roadsidebomb/Polybar-Minibar-3D-Print-Files/Official Releases/Polybar-Minibar v5.0 STLs/Frames/Polybar Les Paul Frame (Bottom).stl

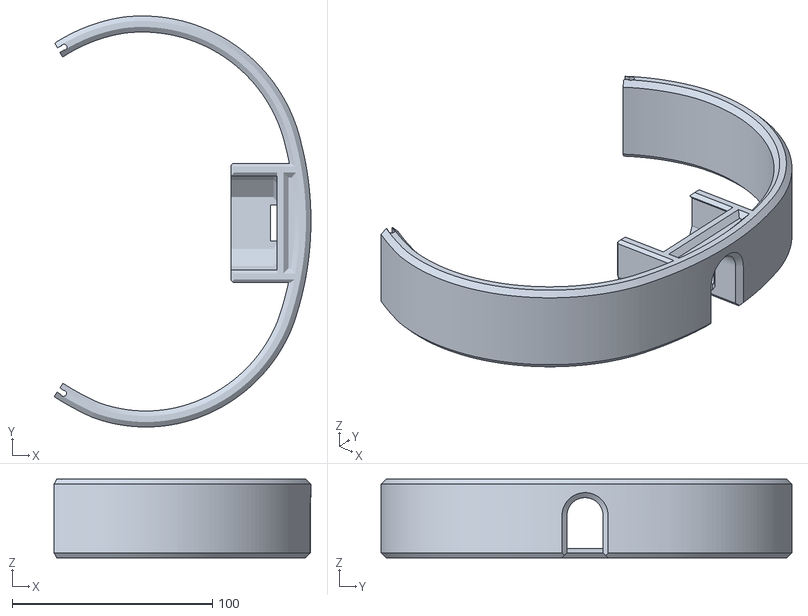
[picture p15: CAD file, 2023-04-15]
Official Releases/Polybar-Minibar v5.0 STLs/Frames/Polybar Les Paul Frame (Bottom).stl
128.2 x 205.1 x 39.4
