roadsidebomb/Polybar-Minibar-3D-Print-Files/Official Releases/Polybar-Minibar v5.0 STLs/Minibar/Minibar Strum Case (Bottom).stl

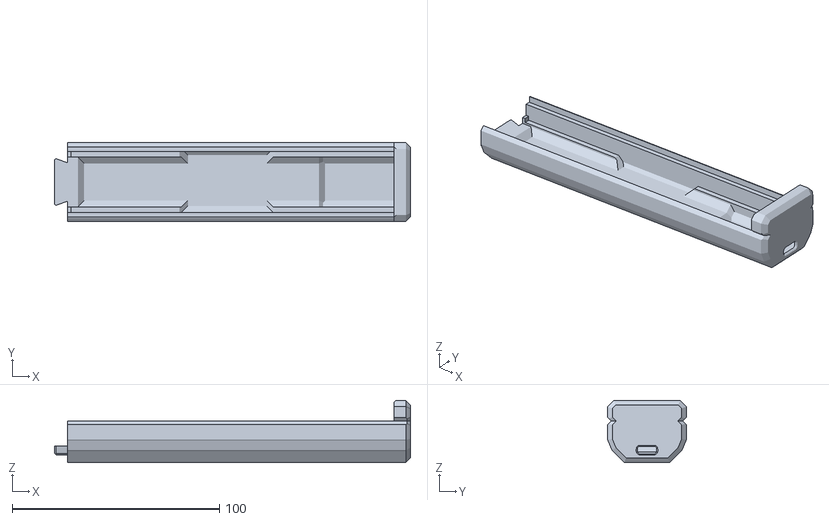
[picture p16: CAD file, 2023-04-15]
Official Releases/Polybar-Minibar v5.0 STLs/Minibar/Minibar Strum Case (Bottom).stl
171.9 x 38.0 x 30.0
