roadsidebomb/Polybar-Minibar-3D-Print-Files/Official Releases/Polybar-Minibar v5.0 STLs/Polybar/Polybar Strum Case (Bottom).stl

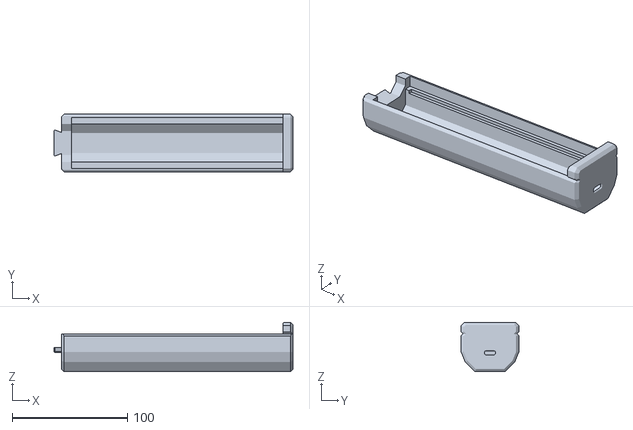
[picture p17: CAD file, 2023-04-15]
Official Releases/Polybar-Minibar v5.0 STLs/Polybar/Polybar Strum Case (Bottom).stl
207.3 x 50.0 x 42.9
