roadsidebomb/Polybar-Minibar-3D-Print-Files/Official Releases/Polybar-Minibar v5.0 STLs/Universal Parts/Large Button.stl

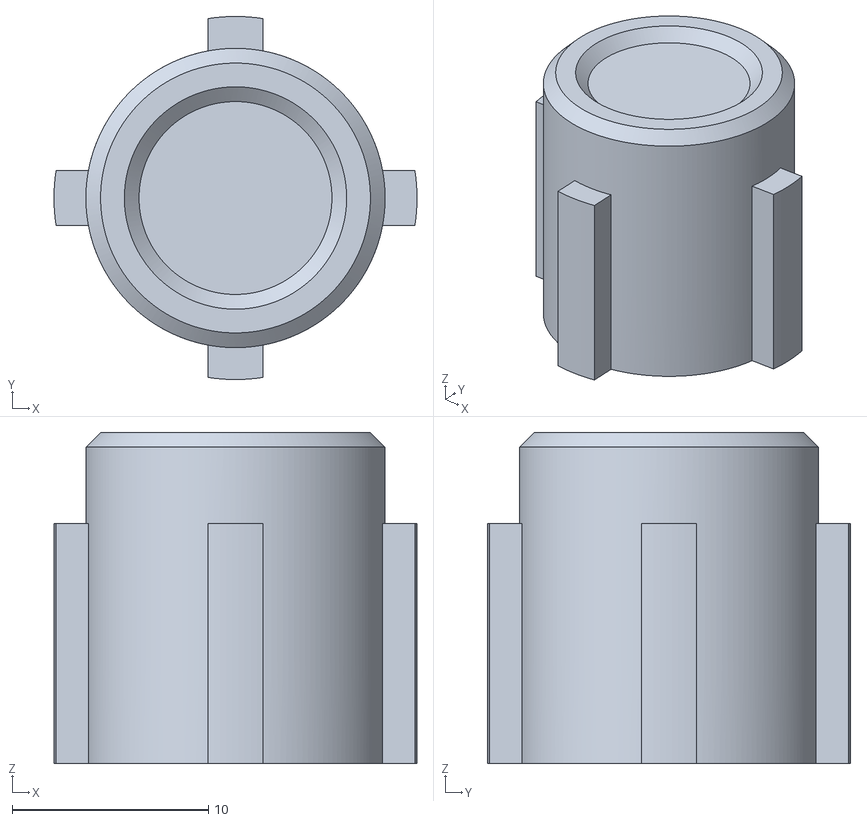
[picture p18: CAD file, 2023-04-15]
Official Releases/Polybar-Minibar v5.0 STLs/Universal Parts/Large Button.stl
18.5 x 18.5 x 16.9
