roadsidebomb/Polybar-Minibar-3D-Print-Files/Official Releases/Polybar-Minibar v5.0 STLs/Universal Shells/Fret Shell (Top).stl

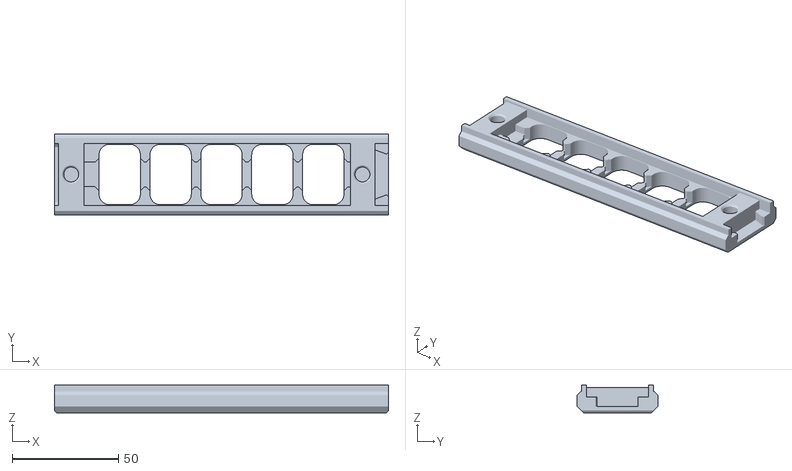
[picture p19: CAD file, 2023-04-15]
Official Releases/Polybar-Minibar v5.0 STLs/Universal Shells/Fret Shell (Top).stl
157.5 x 38.0 x 13.0
