roadsidebomb/Polybar-Minibar-3D-Print-Files/Official Releases/Polybar-Minibar v5.0 STLs/Alternates/5. Large Button/Large Button - .25 down.stl

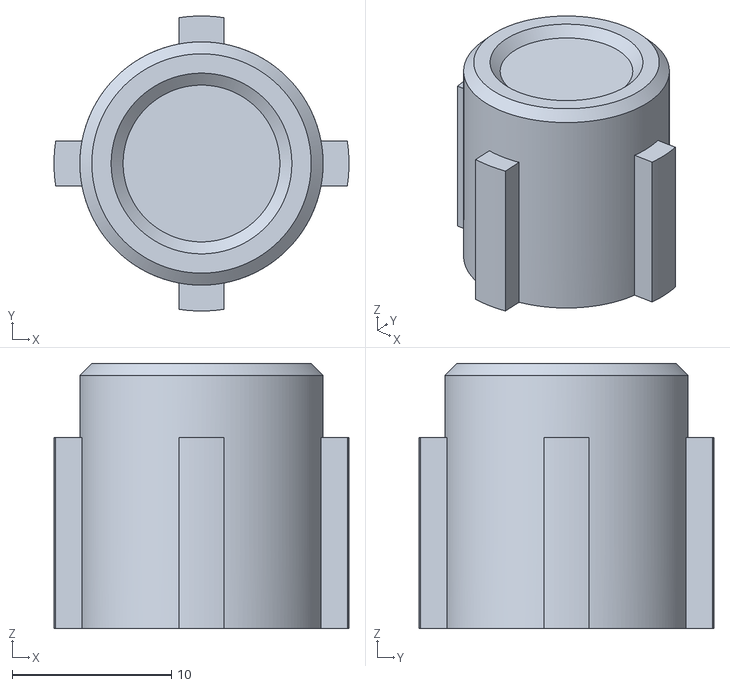
[picture p20: CAD file, 2023-04-15]
Official Releases/Polybar-Minibar v5.0 STLs/Alternates/5. Large Button/Large Button - .25 down.stl
18.5 x 18.5 x 16.6
