roadsidebomb/Polybar-Minibar-3D-Print-Files/Official Releases/Polybar-Minibar v5.0 STLs/Alternates/6. Small Button/Small Button - .25 down.stl

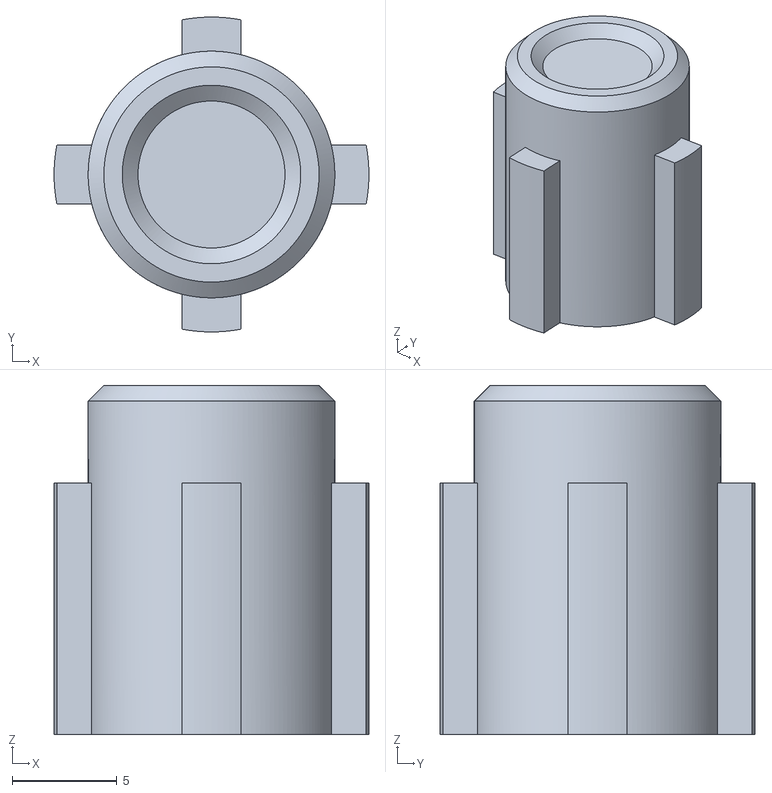
[picture p21: CAD file, 2023-04-15]
Official Releases/Polybar-Minibar v5.0 STLs/Alternates/6. Small Button/Small Button - .25 down.stl
15.0 x 15.0 x 16.6
