roadsidebomb/Polybar-Minibar-3D-Print-Files/Official Releases/Polybar-Minibar v5.0 STLs/Frames/Polybar Xplorer Frame (Bottom).stl

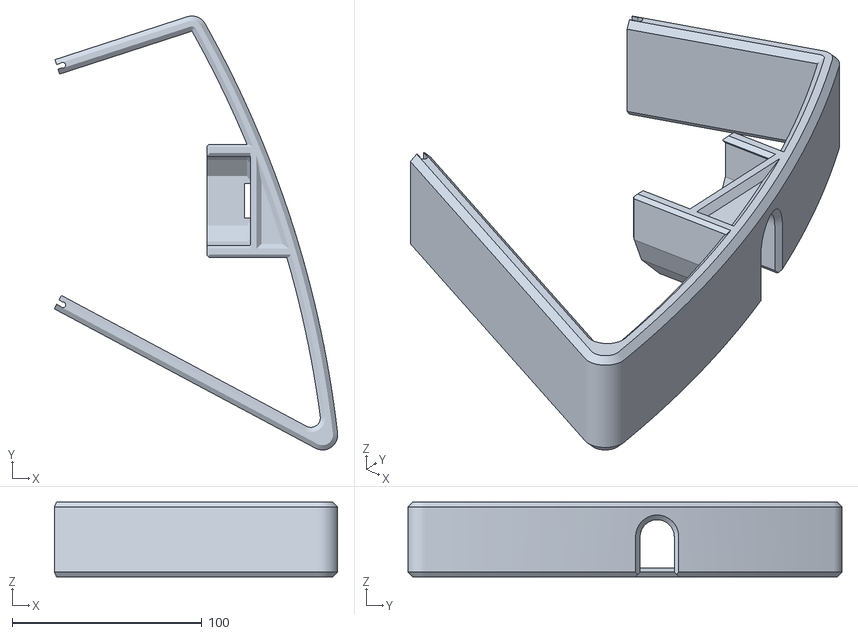
[picture p22: CAD file, 2023-04-15]
Official Releases/Polybar-Minibar v5.0 STLs/Frames/Polybar Xplorer Frame (Bottom).stl
149.4 x 228.7 x 39.4
