roadsidebomb/Polybar-Minibar-3D-Print-Files/Official Releases/Polybar-Minibar v5.0 STLs/Minibar/Minibar Face Plate.stl

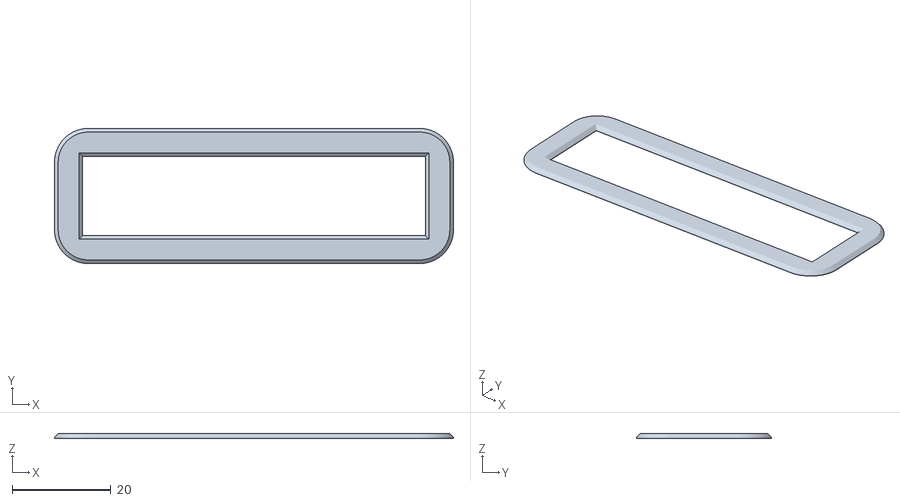
[picture p23: CAD file, 2023-04-15]
Official Releases/Polybar-Minibar v5.0 STLs/Minibar/Minibar Face Plate.stl
80.9 x 27.4 x 1.00
