roadsidebomb/Polybar-Minibar-3D-Print-Files/Official Releases/Polybar-Minibar v5.0 STLs/Polybar/Polybar Face Plate.stl

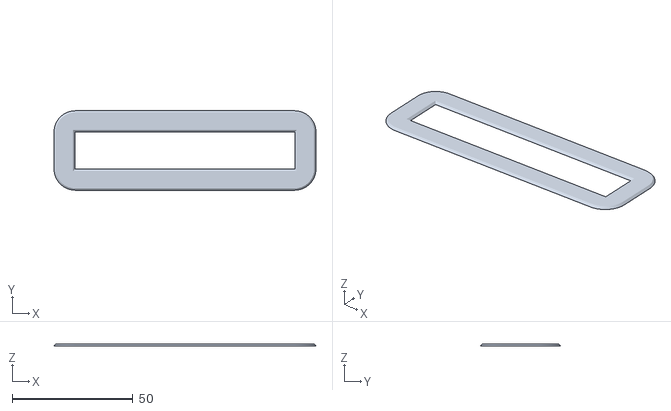
[picture p24: CAD file, 2023-04-15]
Official Releases/Polybar-Minibar v5.0 STLs/Polybar/Polybar Face Plate.stl
108.4 x 32.9 x 1.00
