roadsidebomb/Polybar-Minibar-3D-Print-Files/Official Releases/Polybar-Minibar v5.0 STLs/Universal Parts/Strum Bar Pin.stl

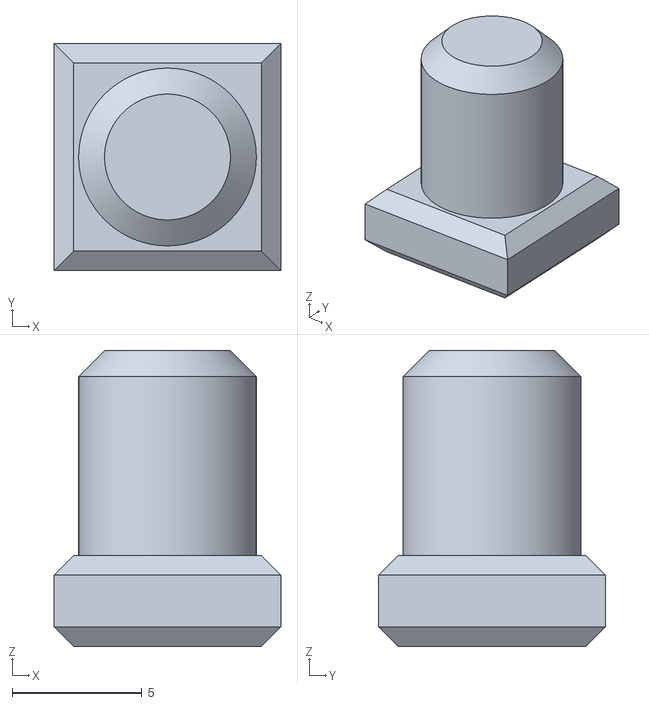
[picture p25: CAD file, 2023-04-15]
Official Releases/Polybar-Minibar v5.0 STLs/Universal Parts/Strum Bar Pin.stl
8.75 x 8.75 x 11.4
