roadsidebomb/Polybar-Minibar-3D-Print-Files/Official Releases/Polybar-Minibar v5.0 STLs/Universal Shells/Long Extension (Bottom).stl

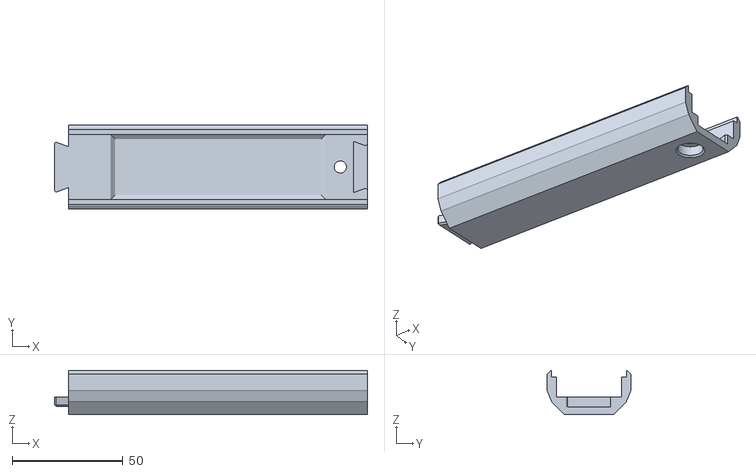
[picture p26: CAD file, 2023-04-15]
Official Releases/Polybar-Minibar v5.0 STLs/Universal Shells/Long Extension (Bottom).stl
141.4 x 38.0 x 20.0
