roadsidebomb/Polybar-Minibar-3D-Print-Files/Official Releases/Polybar-Minibar v5.0 STLs/Frames/Polybar Xplorer Frame (Top).stl

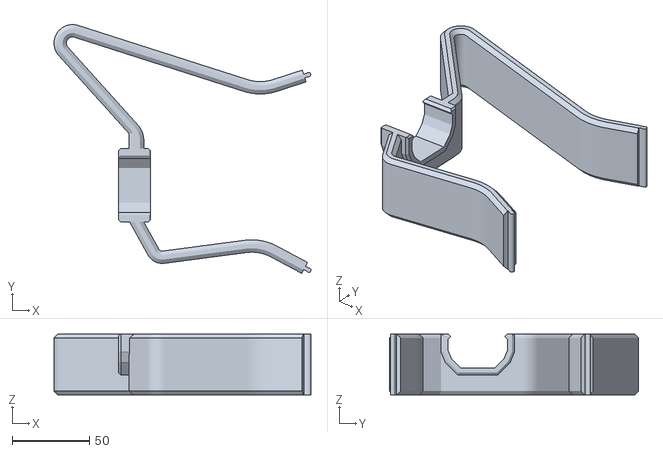
[picture p27: CAD file, 2023-04-15]
Official Releases/Polybar-Minibar v5.0 STLs/Frames/Polybar Xplorer Frame (Top).stl
166.0 x 160.7 x 39.4
