roadsidebomb/Polybar-Minibar-3D-Print-Files/Official Releases/Polybar-Minibar v5.0 STLs/Universal Parts/Strum Bar Pin Retainer Clip.stl

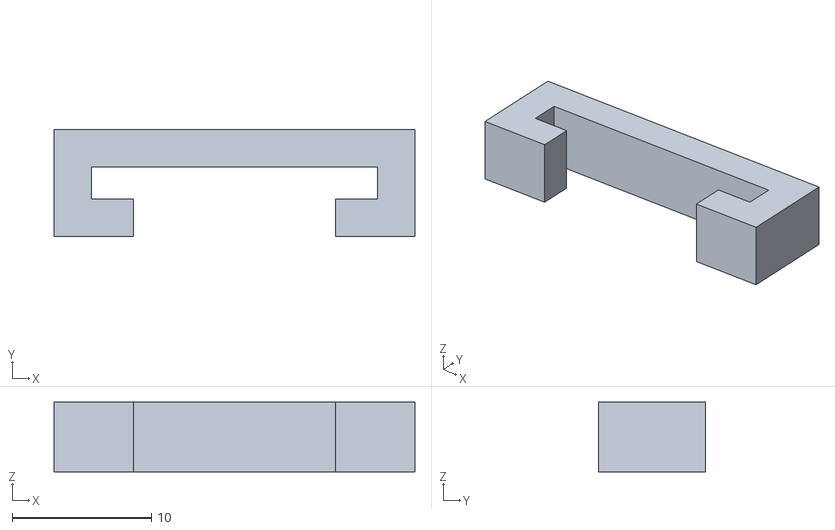
[picture p28: CAD file, 2023-04-15]
Official Releases/Polybar-Minibar v5.0 STLs/Universal Parts/Strum Bar Pin Retainer Clip.stl
25.9 x 7.70 x 5.00
