roadsidebomb/Polybar-Minibar-3D-Print-Files/Official Releases/Polybar-Minibar v5.0 STLs/Frames/Polybar Les Paul Frame (Top).stl

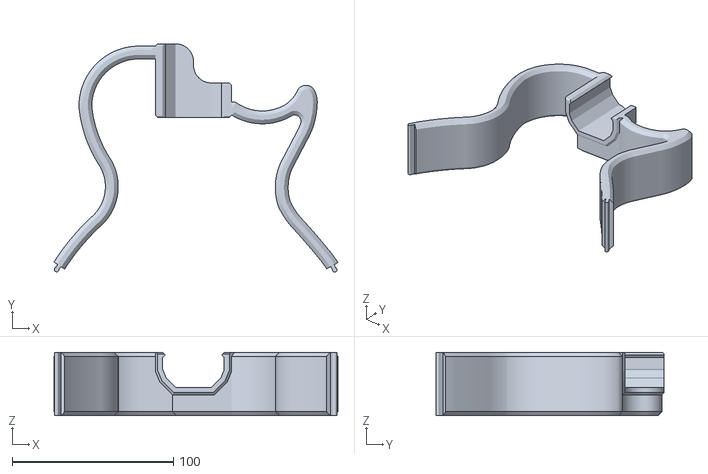
[picture p30: CAD file, 2023-04-15]
Official Releases/Polybar-Minibar v5.0 STLs/Frames/Polybar Les Paul Frame (Top).stl
176.4 x 141.9 x 39.4
