roadsidebomb/Polybar-Minibar-3D-Print-Files/Official Releases/Polybar-Minibar v5.0 STLs/Universal Parts/Fret Insert (Kailh Choc).stl

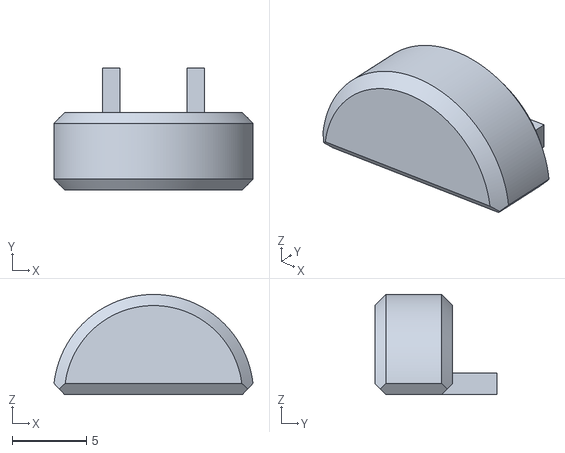
[picture p31: CAD file, 2023-04-15]
Official Releases/Polybar-Minibar v5.0 STLs/Universal Parts/Fret Insert (Kailh Choc).stl
13.4 x 8.25 x 6.75
