roadsidebomb/Polybar-Minibar-3D-Print-Files/Official Releases/Polybar-Minibar v5.0 STLs/Universal Shells/Fret Shell (Bottom).stl

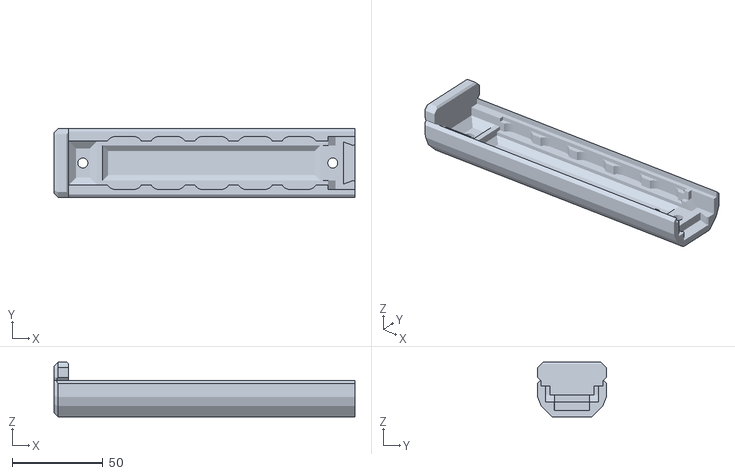
[picture p32: CAD file, 2023-04-15]
Official Releases/Polybar-Minibar v5.0 STLs/Universal Shells/Fret Shell (Bottom).stl
165.5 x 38.0 x 30.0
