roadsidebomb/Polybar-Minibar-3D-Print-Files/Official Releases/Polybar-Minibar v5.0 STLs/Frames/Minibar Xplorer Frame.stl

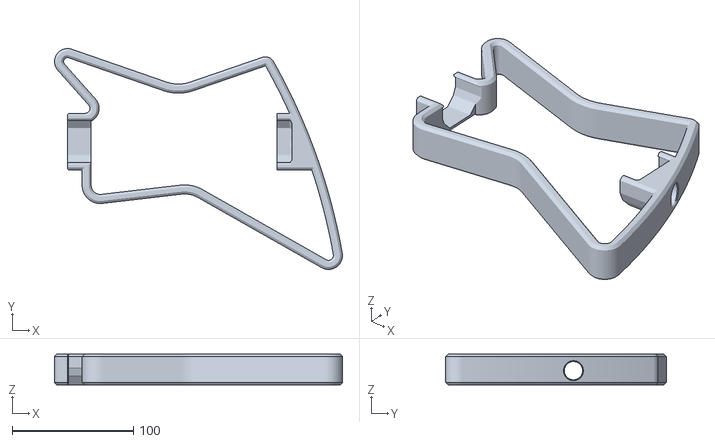
[picture p33: CAD file, 2023-04-15]
Official Releases/Polybar-Minibar v5.0 STLs/Frames/Minibar Xplorer Frame.stl
237.1 x 181.8 x 25.5
