roadsidebomb/Polybar-Minibar-3D-Print-Files/Official Releases/Polybar-Minibar v5.0 STLs/Universal Shells/Short Extension (Top).stl

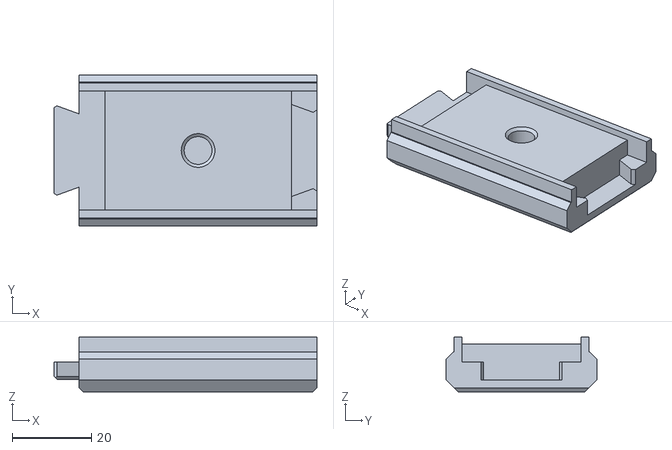
[picture p34: CAD file, 2023-04-15]
Official Releases/Polybar-Minibar v5.0 STLs/Universal Shells/Short Extension (Top).stl
66.4 x 38.0 x 13.8
