roadsidebomb/Polybar-Minibar-3D-Print-Files/Official Releases/Polybar-Minibar v5.0 STLs/Frames/Minibar Banjo Frame.stl

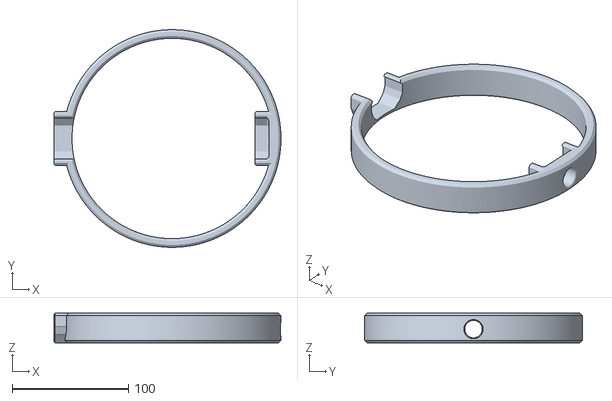
[picture p35: CAD file, 2023-04-15]
Official Releases/Polybar-Minibar v5.0 STLs/Frames/Minibar Banjo Frame.stl
195.0 x 187.0 x 25.5
