roadsidebomb/Polybar-Minibar-3D-Print-Files/Official Releases/Polybar-Minibar v5.0 STLs/Universal Parts/Fret Insert (MX Cherry).stl

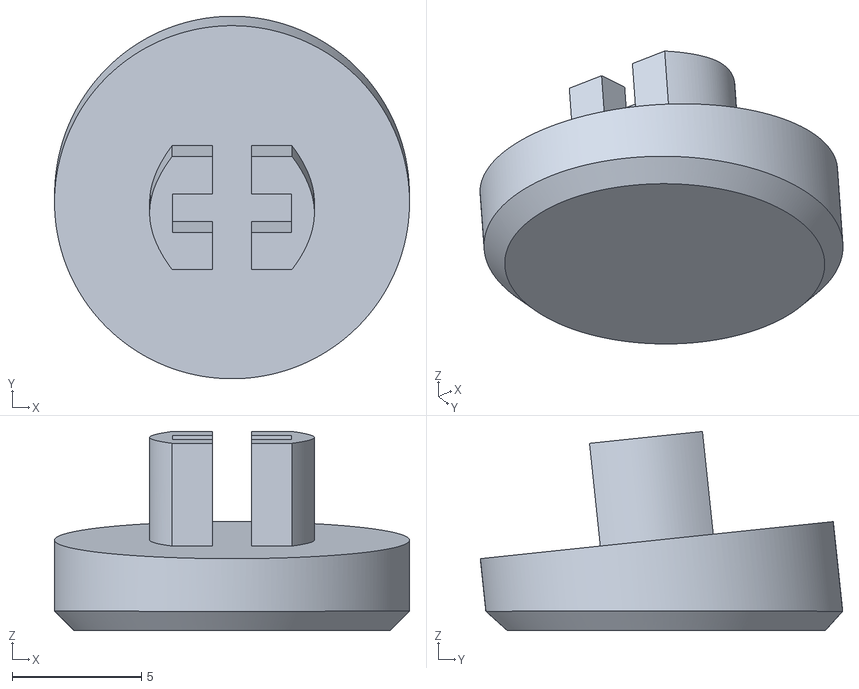
[picture p36: CAD file, 2023-04-15]
Official Releases/Polybar-Minibar v5.0 STLs/Universal Parts/Fret Insert (MX Cherry).stl
13.7 x 14.0 x 7.71
